Michael-Manning/E-Paper-Climate-Logger/CAD/V2/clip.png

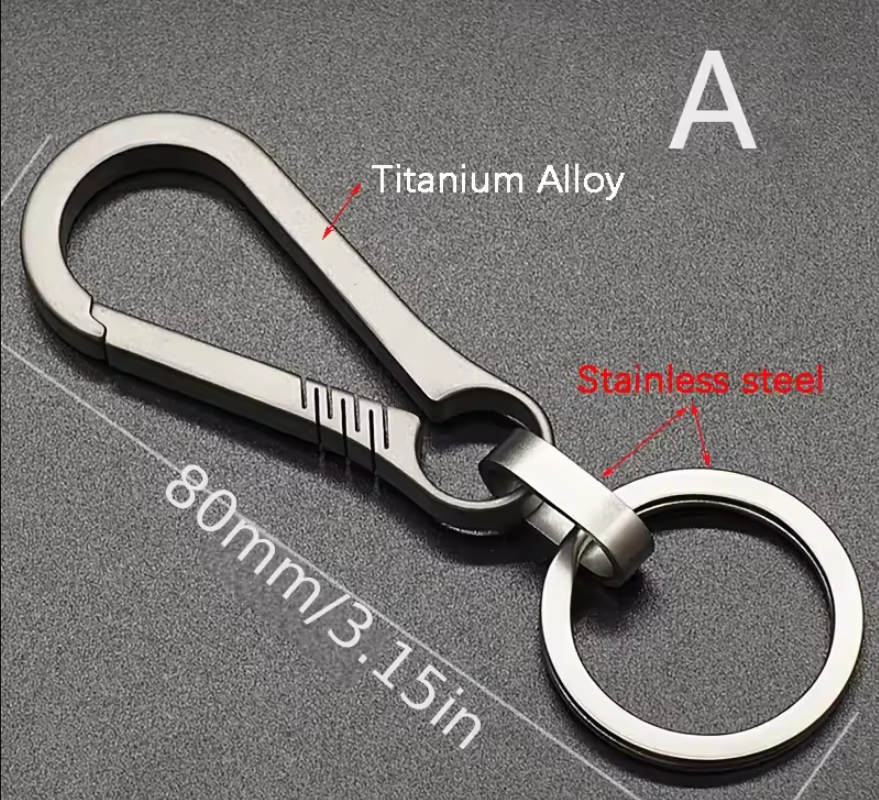
CAD/V2/clip.png
