Michael-Manning/E-Paper-Climate-Logger/firmware/bitmapGenerator/images/dead_battery_screen.bmp

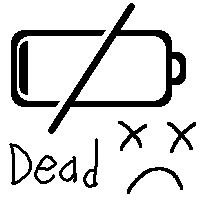
firmware/bitmapGenerator/images/dead_battery_screen.bmp
