Michael-Manning/E-Paper-Climate-Logger/firmware/bitmapGenerator/images/night_mode_screen.bmp

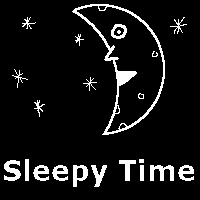
firmware/bitmapGenerator/images/night_mode_screen.bmp
