Michael-Manning/E-Paper-Climate-Logger/firmware/bitmapGenerator/images/power_off_screen.bmp

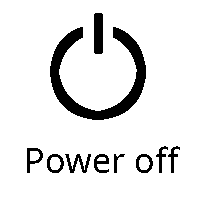
firmware/bitmapGenerator/images/power_off_screen.bmp
